AmesisProject/012-Amesis-ColdStartE85/Hardware/v0.01_dev/Visu/IMG_6671.JPG

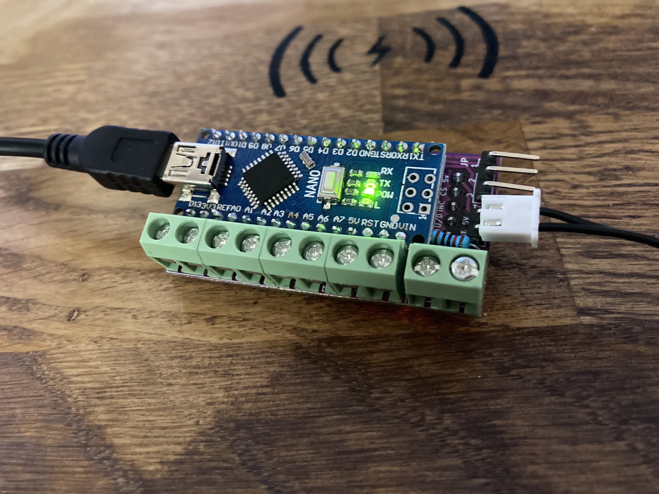
Hardware/v0.01_dev/Visu/IMG_6671.JPG
