AmesisProject/012-Amesis-ColdStartE85/Image/algorithme.jpg

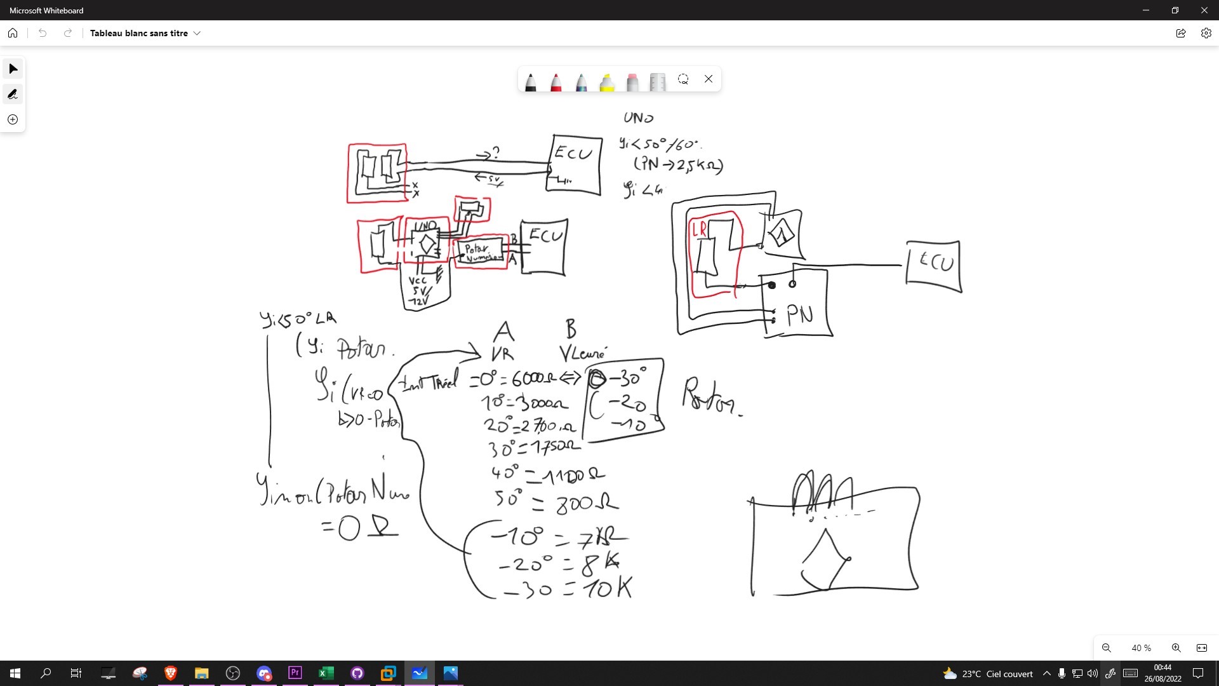
Image/algorithme.jpg
