AmesisProject/012-Amesis-ColdStartE85/Image/DS18B20/sonde temperature ds18b20.jpg

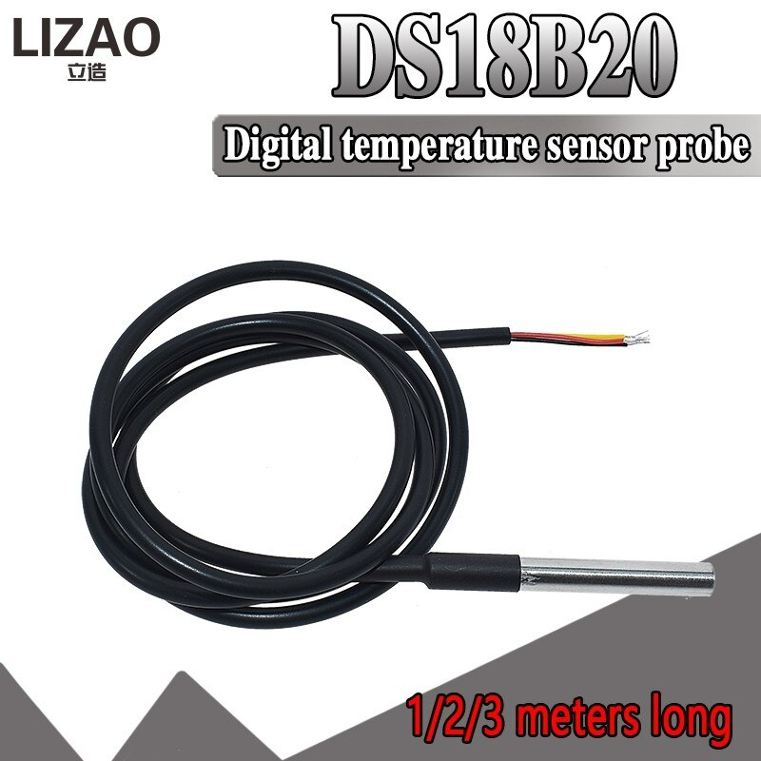
Image/DS18B20/sonde temperature ds18b20.jpg
