AmesisProject/012-Amesis-ColdStartE85/Image/Potentiomètre Numérique/el.jpg

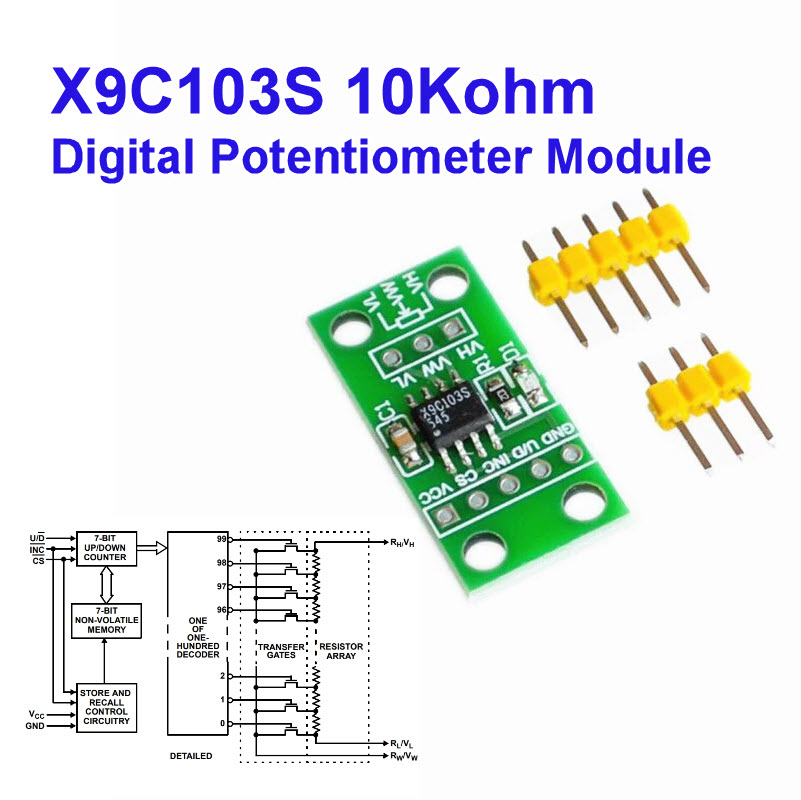
Image/Potentiomètre Numérique/el.jpg
