AmesisProject/012-Amesis-ColdStartE85/Image/Sondes de température/Sonde 2 poles/2d linea.jpg

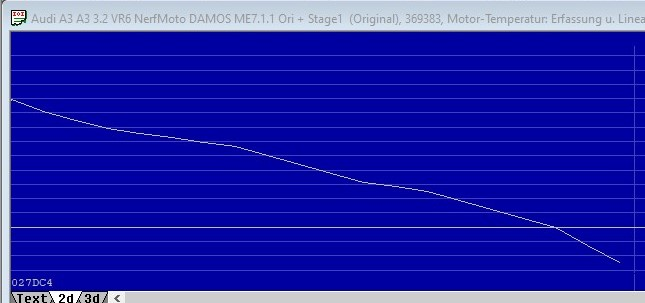
Image/Sondes de température/Sonde 2 poles/2d linea.jpg
