AmesisProject/012-Amesis-ColdStartE85/Image/Sondes de température/Sonde 2 poles/connecteur 2 poles male-femelle 1J0973702.jpg

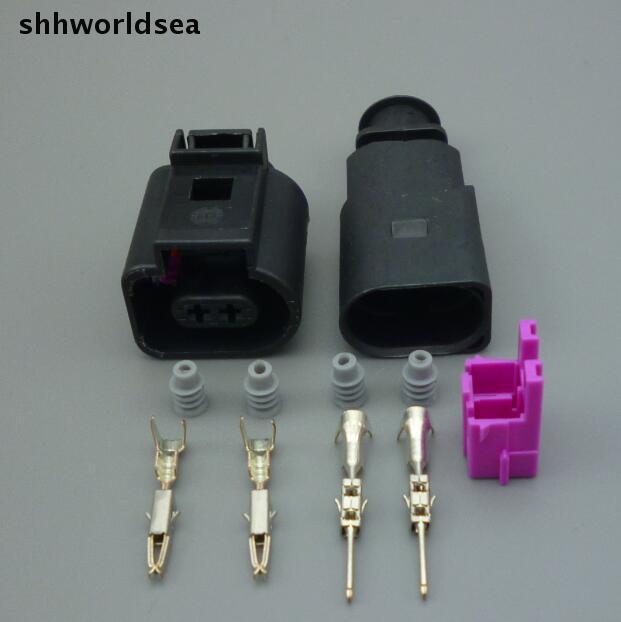
Image/Sondes de température/Sonde 2 poles/connecteur 2 poles male-femelle 1J0973702.jpg
