AmesisProject/012-Amesis-ColdStartE85/Image/Sondes de température/Sonde 2 poles/Linea Sonde T LR.jpg

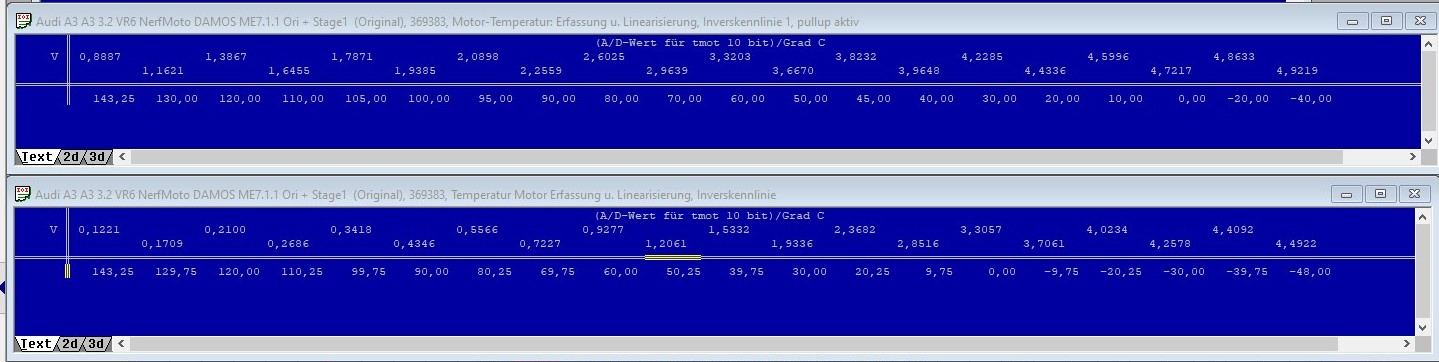
Image/Sondes de température/Sonde 2 poles/Linea Sonde T LR.jpg
