AmesisProject/012-Amesis-ColdStartE85/Image/Sondes de température/Sonde 2 poles/ols.jpg

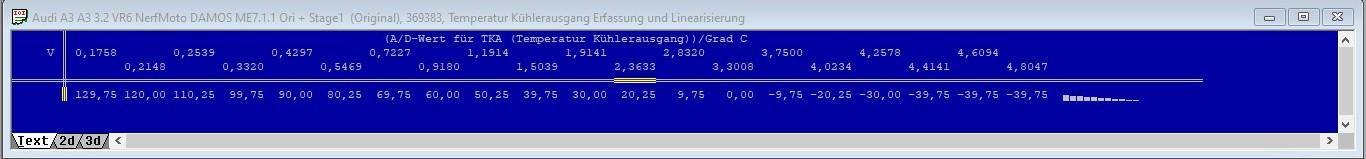
Image/Sondes de température/Sonde 2 poles/ols.jpg
