AmesisProject/012-Amesis-ColdStartE85/Image/Sondes de température/Sonde 2 poles/sonde temperature 06A919501A.webp

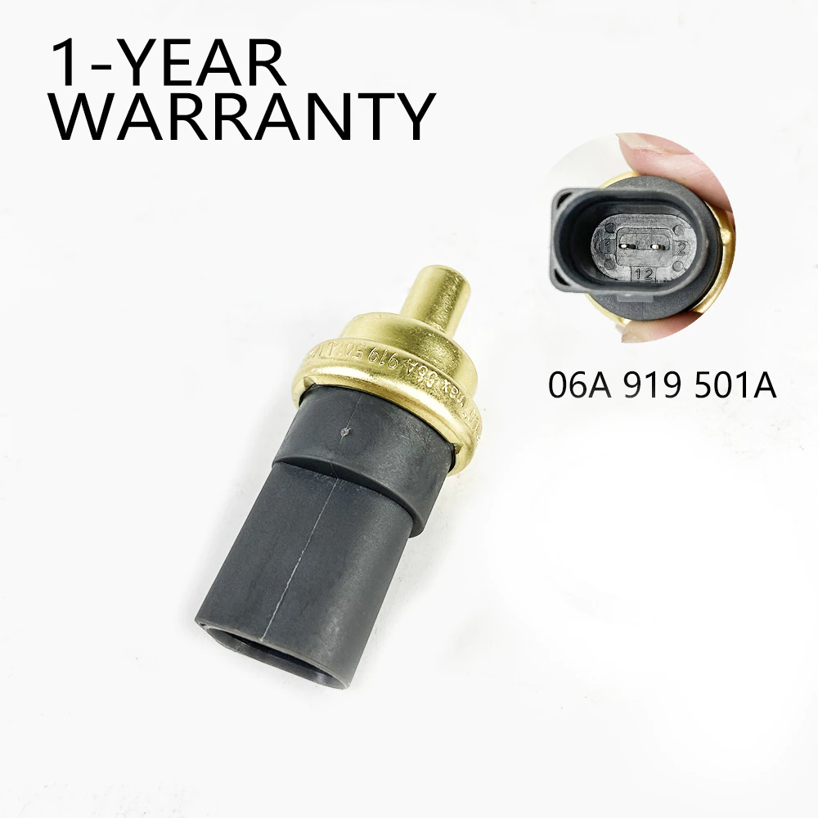
Image/Sondes de température/Sonde 2 poles/sonde temperature 06A919501A.webp
