AmesisProject/012-Amesis-ColdStartE85/Image/Sondes de température/Sonde 2 poles/sonde-temperature-liquide-de-refroidissement-discovery-freelander-range-rover-td4.png

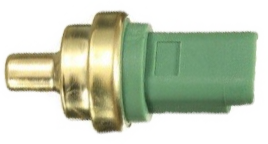
Image/Sondes de température/Sonde 2 poles/sonde-temperature-liquide-de-refroidissement-discovery-freelander-range-rover-td4.png
