AmesisProject/012-Amesis-ColdStartE85/Image/Sondes de température/Sonde 2 poles/vue eclatax sonde temperature ldr (3,2l).png

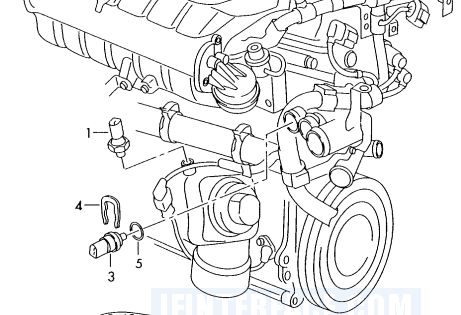
Image/Sondes de température/Sonde 2 poles/vue eclatax sonde temperature ldr (3,2l).png
