AmesisProject/012-Amesis-ColdStartE85/Image/Sondes de température/Sonde 4 poles/connecteur 4 poles male-femelle  4B0973712.jpg

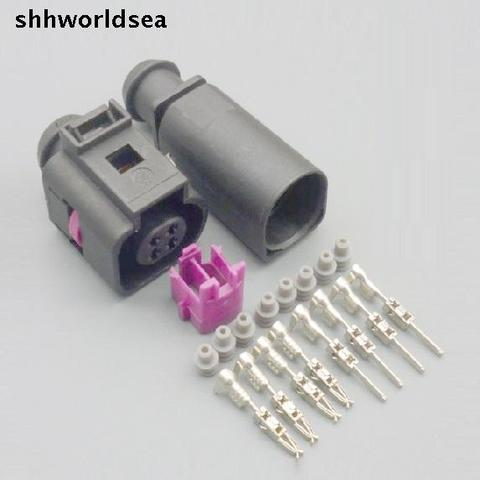
Image/Sondes de température/Sonde 4 poles/connecteur 4 poles male-femelle 4B0973712.jpg
