AmesisProject/012-Amesis-ColdStartE85/Image/Sondes de température/Sonde 4 poles/courbe sonde temperature.jpg

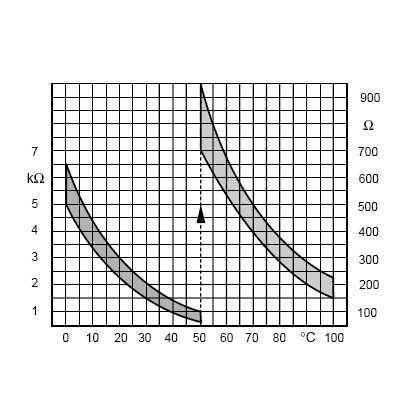
Image/Sondes de température/Sonde 4 poles/courbe sonde temperature.jpg
