AmesisProject/012-Amesis-ColdStartE85/Image/Sondes de température/Sonde 4 poles/data sonde ot.jpg

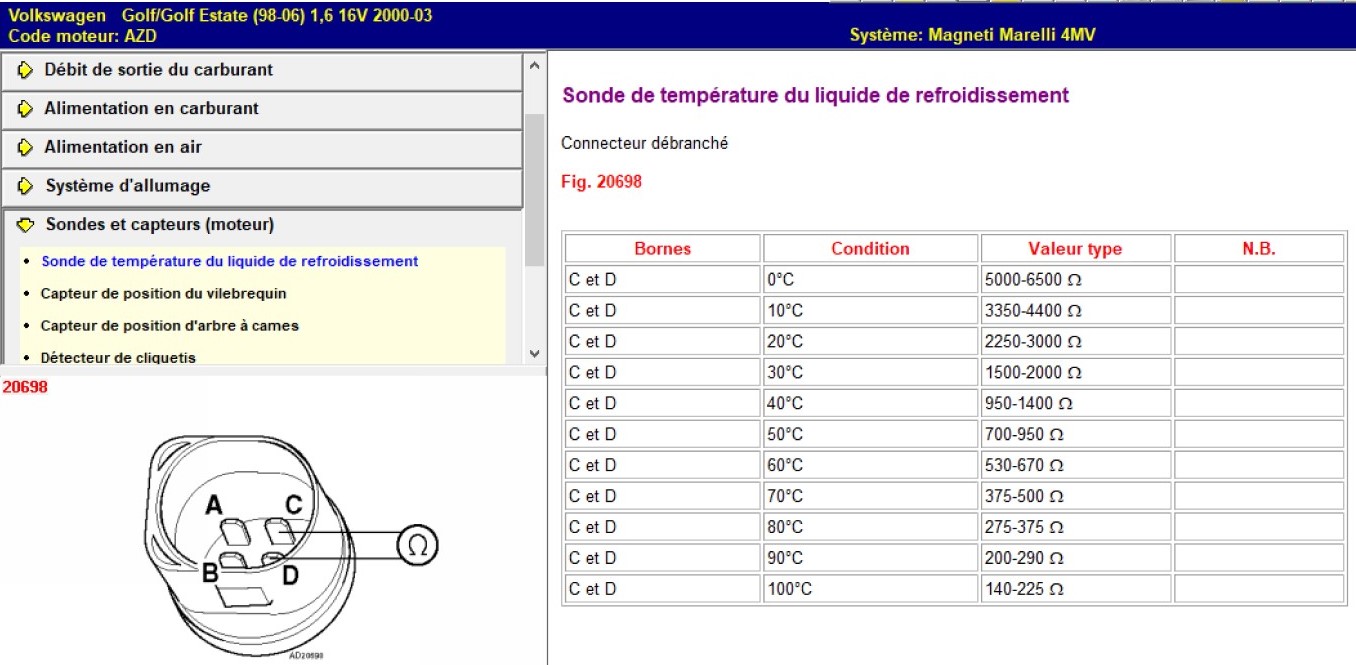
Image/Sondes de température/Sonde 4 poles/data sonde ot.jpg
