AmesisProject/012-Amesis-ColdStartE85/Image/Sondes de température/Sonde 4 poles/sonde de temperature ldr 059919501A.jpg

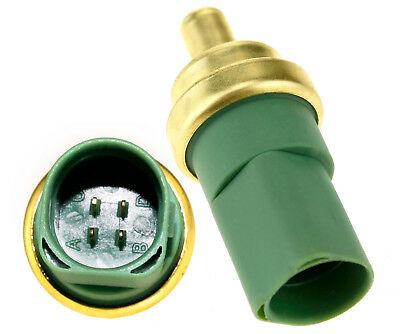
Image/Sondes de température/Sonde 4 poles/sonde de temperature ldr 059919501A.jpg
