AmesisProject/012-Amesis-ColdStartE85/Image/Sondes de température/Sonde 4 poles/vue éclatax sonde température ldr.png

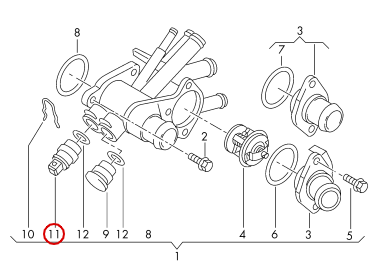
Image/Sondes de température/Sonde 4 poles/vue éclatax sonde température ldr.png
