AmesisProject/012-Amesis-ColdStartE85/Image/Sondes de température/thermistance 10K B3950/M3 10K B3950 .jpg

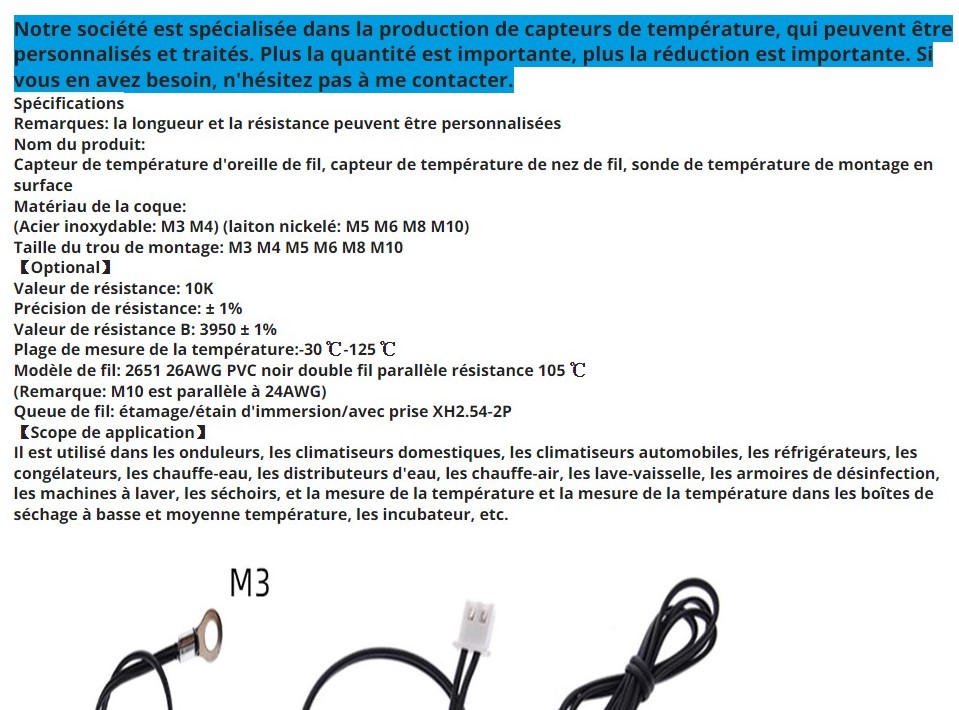
Image/Sondes de température/thermistance 10K B3950/M3 10K B3950 .jpg
