AmesisProject/012-Amesis-ColdStartE85/Manuel d'utilisation/cluster.png

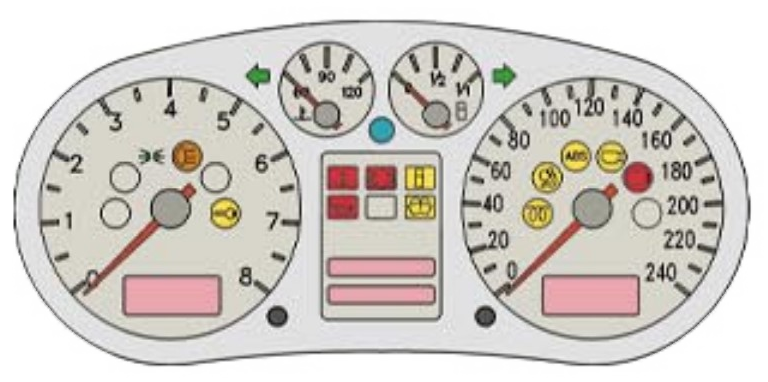
Manuel d'utilisation/cluster.png
