AmesisProject/012-Amesis-ColdStartE85/Manuel d'utilisation/ECU.png

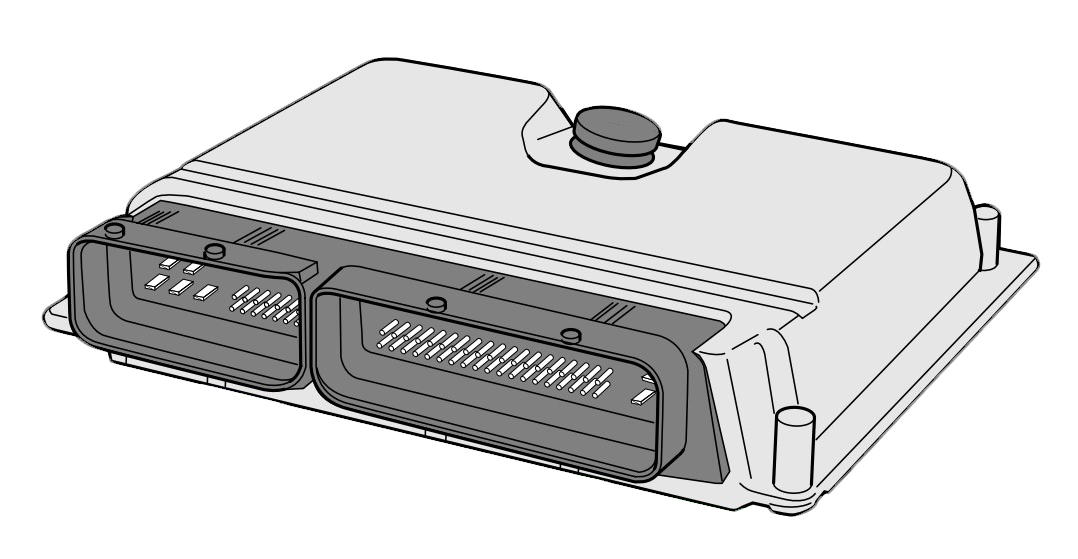
Manuel d'utilisation/ECU.png
