AmesisProject/012-Amesis-ColdStartE85/Schémas électrique/SharedScreenshot.jpg

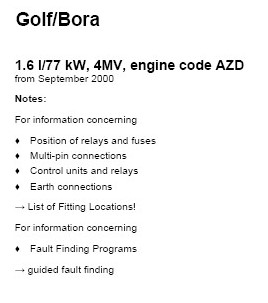
Schémas électrique/SharedScreenshot.jpg
