AmesisProject/012-Amesis-ColdStartE85/Image/DS18B20/montage_ds18b20_schéma.jpg

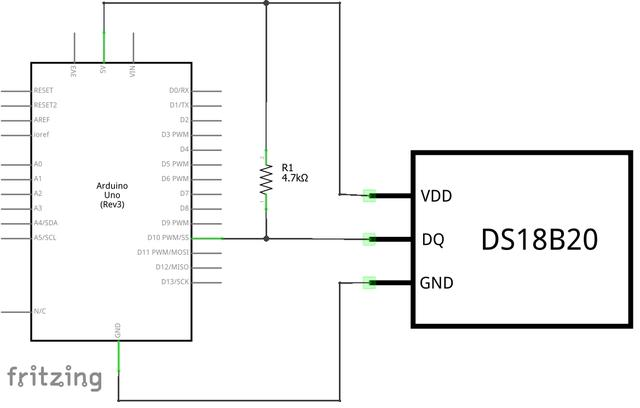
Image/DS18B20/montage_ds18b20_schéma.jpg
