AmesisProject/012-Amesis-ColdStartE85/Hardware/Kicad/Laster/012-Amesis-ColdSartE85/012-Amesis-ColdSartE85.kicad_sch

## KiCad design Hardware/Kicad/Laster/012-Amesis-ColdSartE85/012-Amesis-ColdSartE85.kicad_sch (2022-10-03)


Parts:
A1: Arduino_Nano_v3.x; Arduino_Nano
G2/G62_InPut_IAT1, G2/G62_OutPut_IAT1: Conn_01x04_Male; TerminalBlock_bornier-4_P5.08mm
J1: Screw_Terminal_01x02; TerminalBlock_bornier-2_P5.08mm
J2: Conn_01x05_Female; PinSocket_1x05_P2.54mm_Vertical
J3: Conn_01x03_Female; PinSocket_1x03_P2.54mm_Vertical
Jumpers_Option1: Conn_01x03_Male; PinHeader_1x03_P2.54mm_Vertical
R1: R10K; R_Axial_DIN0204_L3.6mm_D1.6mm_P5.08mm_Horizontal
TH1: Thermistor; PinHeader_1x02_P2.54mm_Vertical

Connections:
GND: A1.4 (GND), A1.29 (GND), J1.1, J2.5, Jumpers_Option1.2, R1.2
unnamed: A1.5 (D2), J2.3
unnamed: A1.6 (D3), J2.4
unnamed: A1.7 (D4), J2.2
unnamed: A1.13 (D10), Jumpers_Option1.1
unnamed: A1.15 (D12), Jumpers_Option1.3
unnamed: A1.26 (A7), R1.1, TH1.2
unnamed: A1.27 (+5V), J2.1, TH1.1
unnamed: A1.30 (VIN), J1.2
unnamed: G2/G62_InPut_IAT1.1, G2/G62_OutPut_IAT1.1
unnamed: G2/G62_InPut_IAT1.2, G2/G62_OutPut_IAT1.2
unnamed: G2/G62_InPut_IAT1.3, J3.2
unnamed: G2/G62_InPut_IAT1.4, G2/G62_OutPut_IAT1.4
unnamed: G2/G62_OutPut_IAT1.3, J3.1
